BrettHallen/Rhythm_Keyboard/Images/Rhythm_Keyboard_Display.jpeg

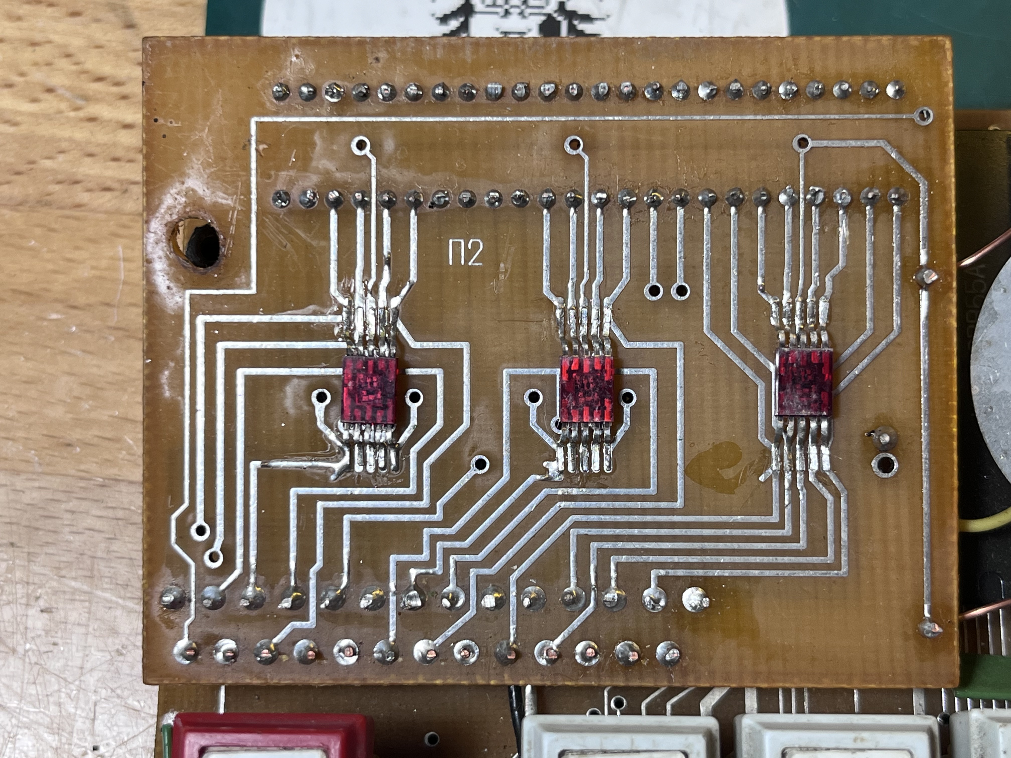
Images/Rhythm_Keyboard_Display.jpeg
