BrettHallen/Rhythm_Keyboard/Images/Rhythm_Keyboard_Expansion.jpeg

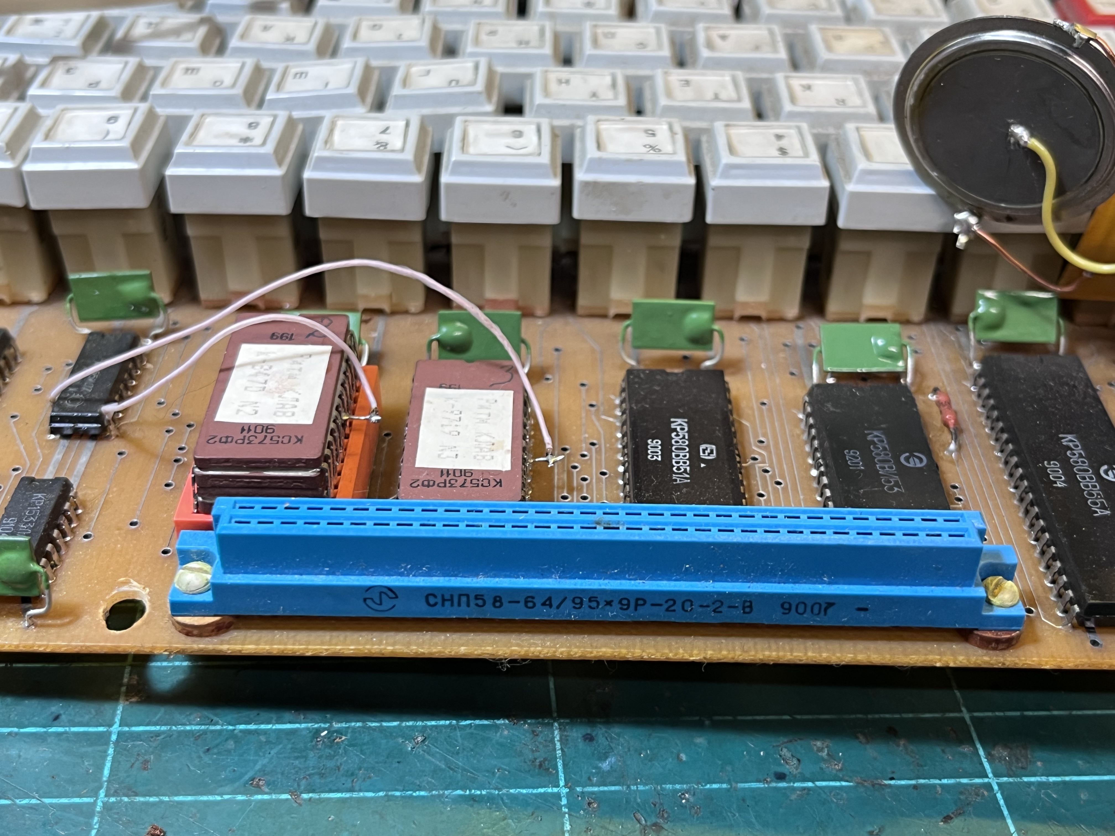
Images/Rhythm_Keyboard_Expansion.jpeg
