BrettHallen/Rhythm_Keyboard/Images/Rhythm_Keyboard_Motherboard01a.jpeg

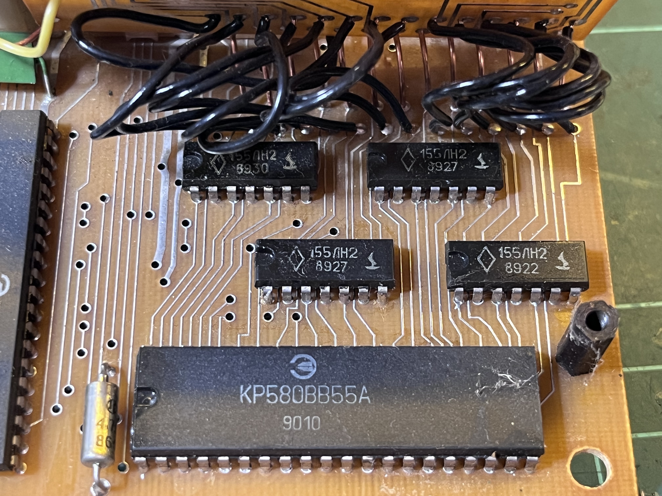
Images/Rhythm_Keyboard_Motherboard01a.jpeg
