BrettHallen/Rhythm_Keyboard/Images/Rhythm_Keyboard_Motherboard04.jpeg

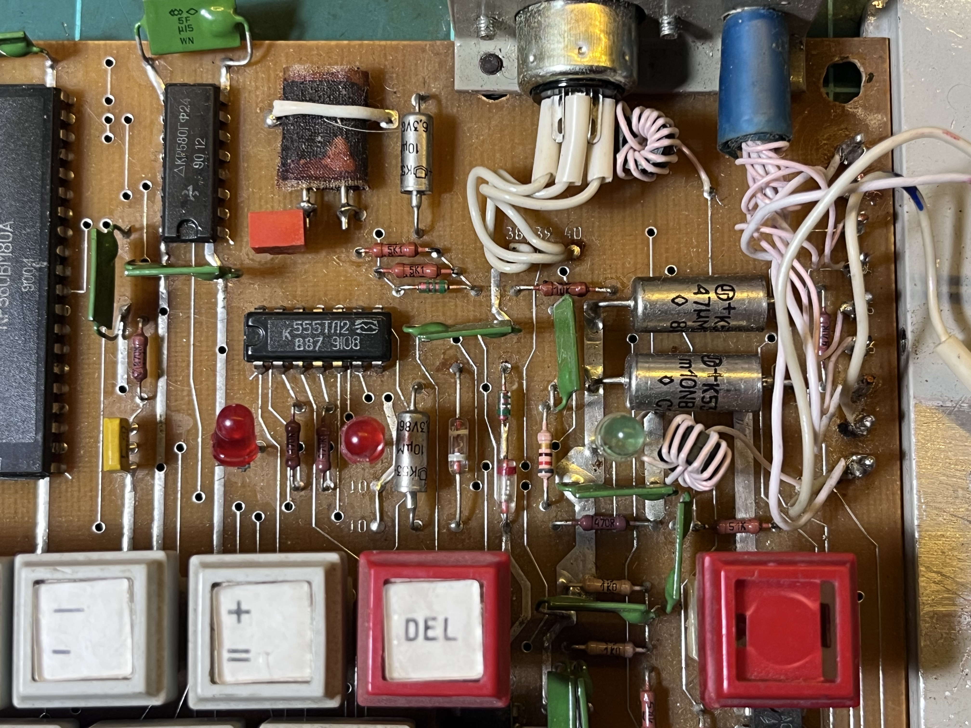
Images/Rhythm_Keyboard_Motherboard04.jpeg
