BrettHallen/Rhythm_Keyboard/Images/Rhythm_Keyboard_Motherboard05.jpeg

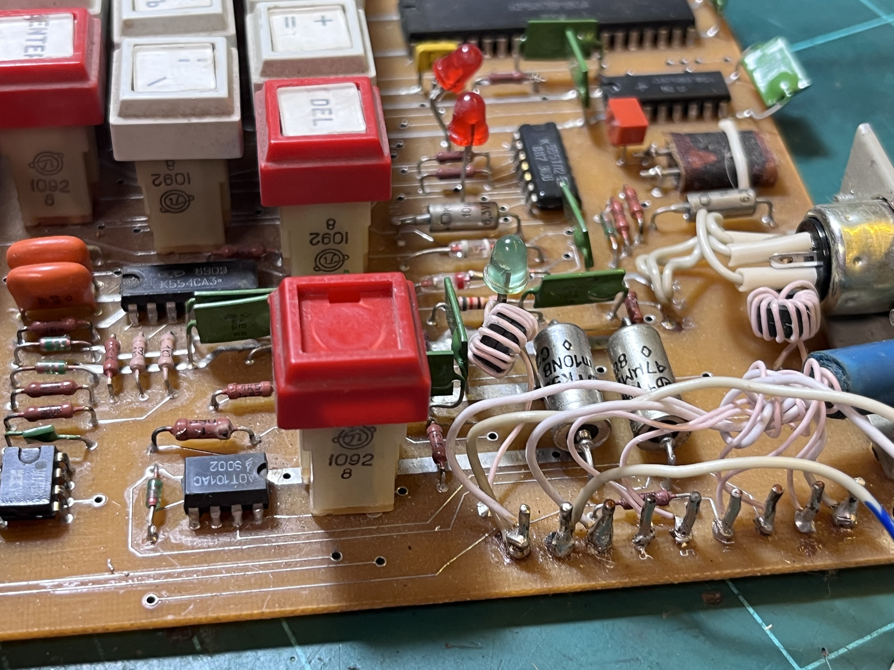
Images/Rhythm_Keyboard_Motherboard05.jpeg
