BrettHallen/Rhythm_Keyboard/Images/Rhythm_Keyboard_Motherboard06.jpeg

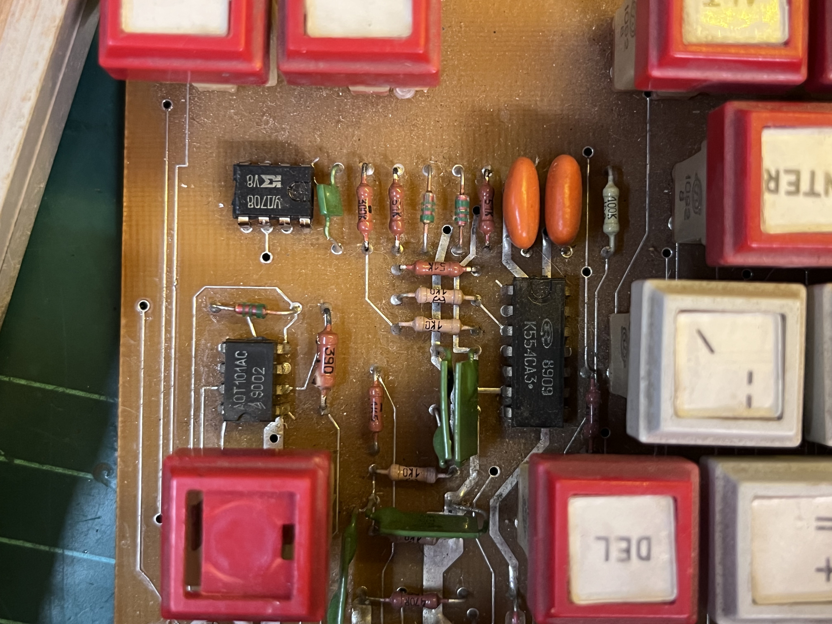
Images/Rhythm_Keyboard_Motherboard06.jpeg
