BrettHallen/Rhythm_Keyboard/Images/Rhythm_Keyboard_Motherboard07.jpeg

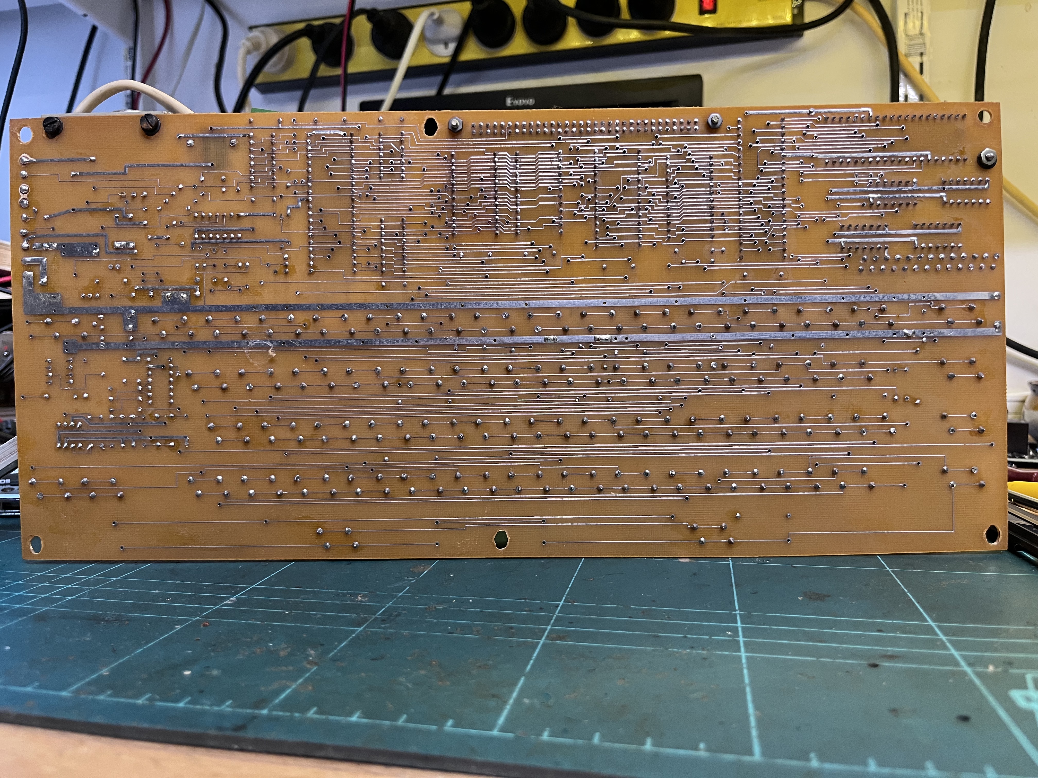
Images/Rhythm_Keyboard_Motherboard07.jpeg
