BrettHallen/Rhythm_Keyboard/Images/Rhythm_Keyboard_Motherboard08.jpeg

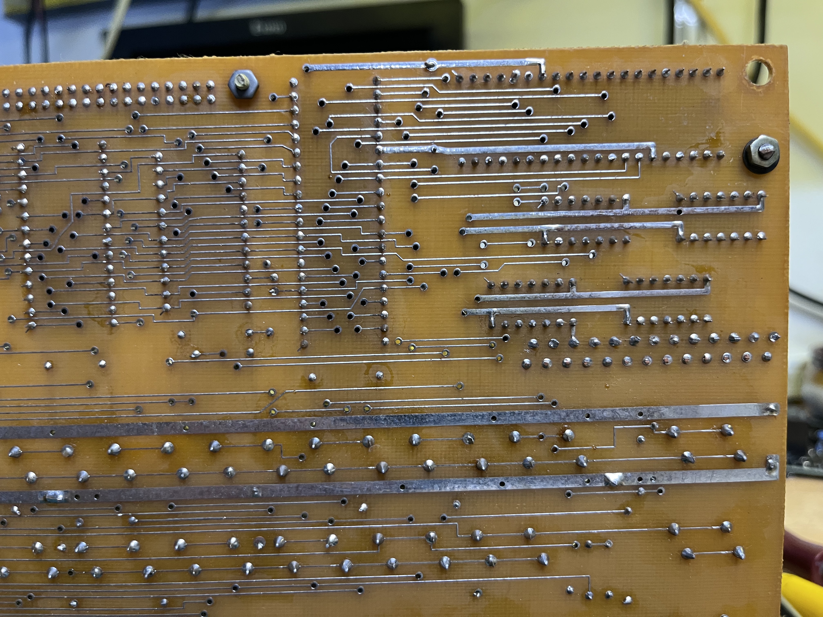
Images/Rhythm_Keyboard_Motherboard08.jpeg
