BrettHallen/Rhythm_Keyboard/Images/Rhythm_Keyboard_Motherboard11.jpeg

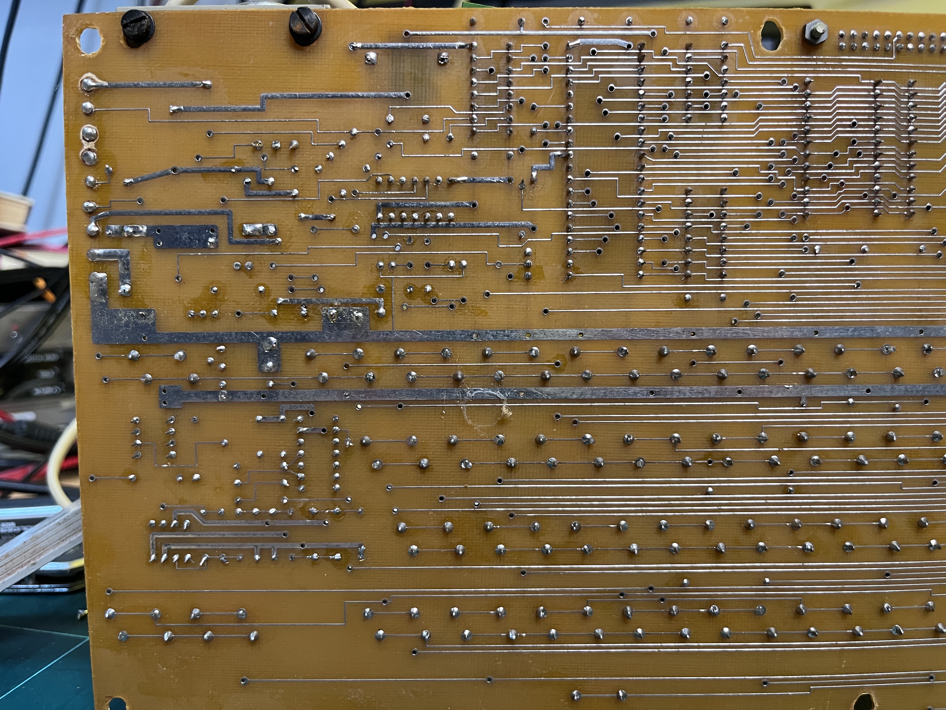
Images/Rhythm_Keyboard_Motherboard11.jpeg
