BrettHallen/Rhythm_Keyboard/Images/Rhythm_Keyboard_ROM_N2.jpeg

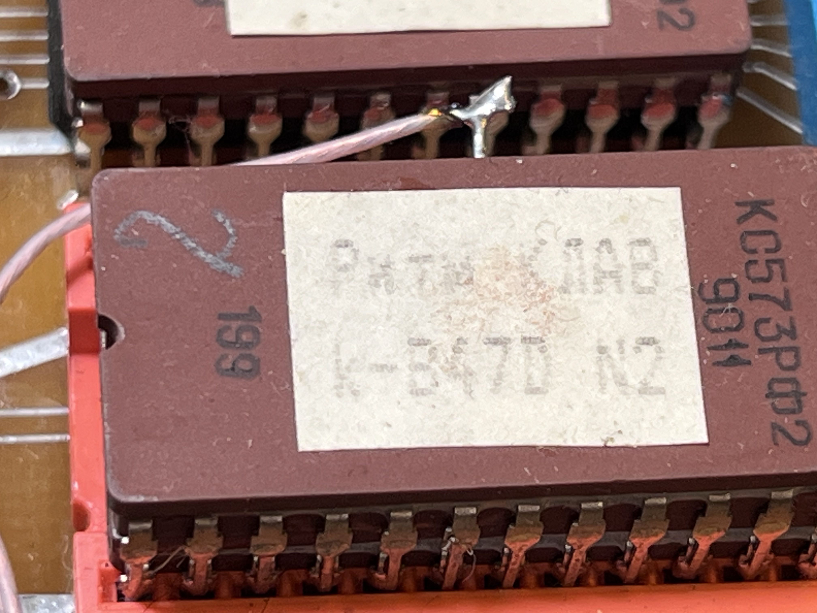
Images/Rhythm_Keyboard_ROM_N2.jpeg
