BrettHallen/Rhythm_Keyboard/Images/Rhythm_Keyboard_ROM_Select.jpeg

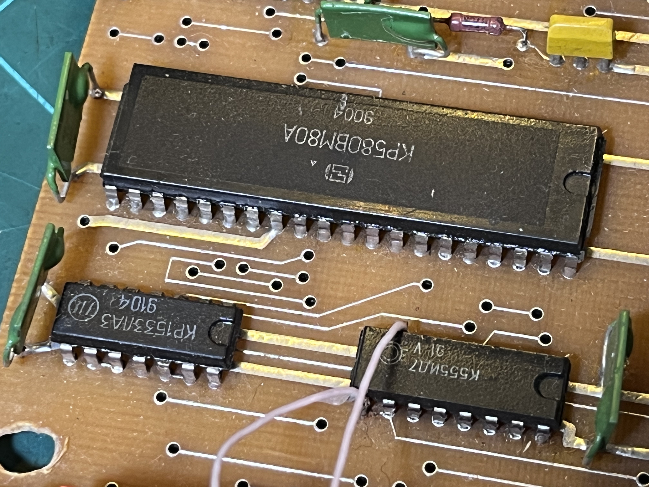
Images/Rhythm_Keyboard_ROM_Select.jpeg
