BrettHallen/Rhythm_Keyboard/Images/Rhythm_Keyboard_ROMs1.jpeg

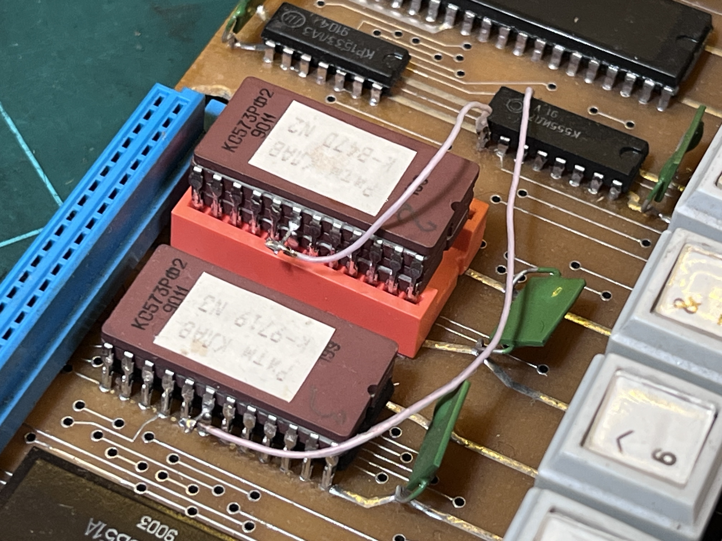
Images/Rhythm_Keyboard_ROMs1.jpeg
