BrettHallen/Rhythm_Keyboard/Images/Rhythm_Keyboard_Speaker_Transistor.jpeg

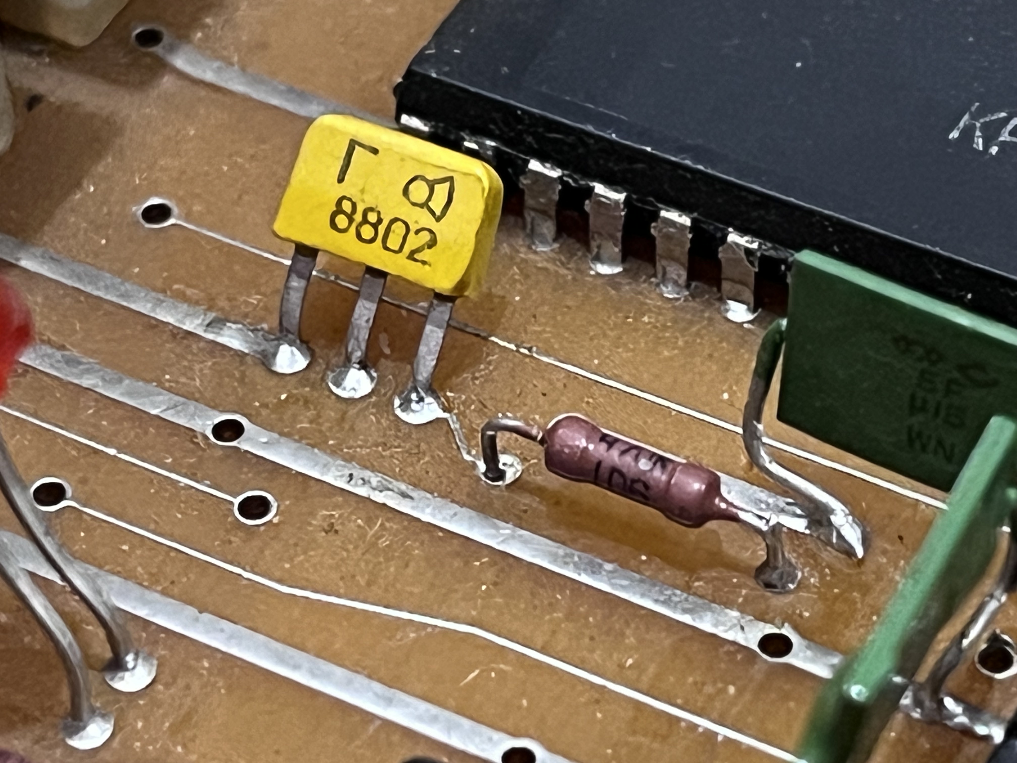
Images/Rhythm_Keyboard_Speaker_Transistor.jpeg
