BrettHallen/Rhythm_Keyboard/Images/Rhythm_Keyboard_SRAM.jpeg

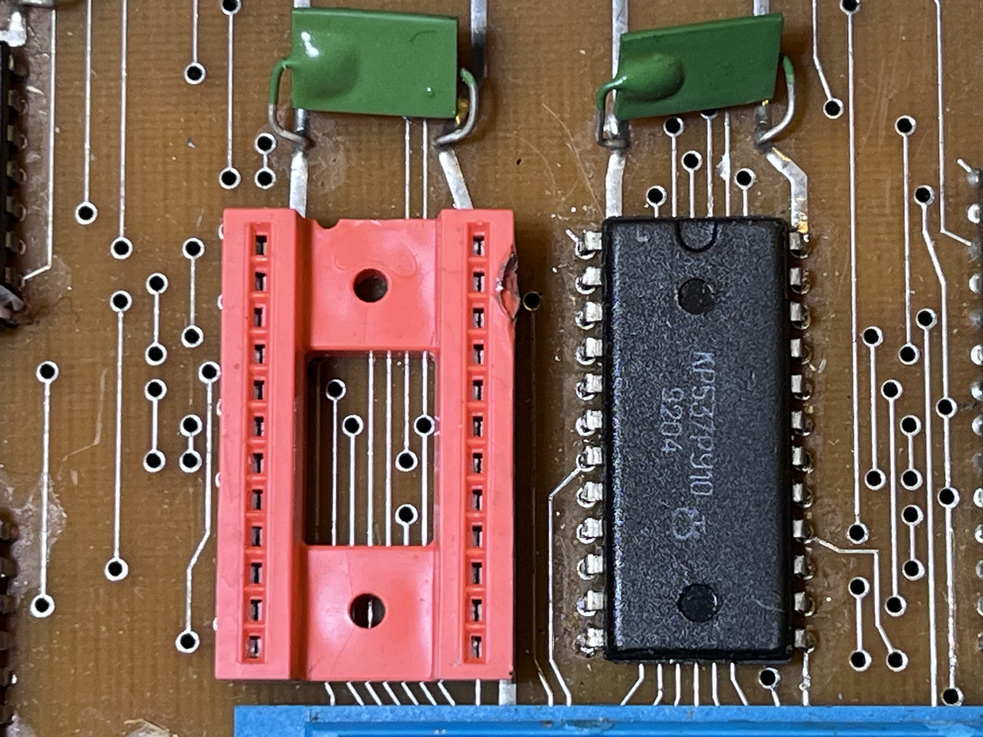
Images/Rhythm_Keyboard_SRAM.jpeg
