BrettHallen/Rhythm_Keyboard/ROMs/RITM_KLAV_N1.ASM

0000 c3 b4 39		jmp 39b4h
0003 f3      		di 
0004 31 00 10		lxi sp, 1000h
0007 3e 98   		mvi a, 98h
0009 32 03 18		sta 1803h
000c 3e 80   		mvi a, 80h
000e 32 03 28		sta 2803h
0011 3e 36   		mvi a, 36h
0013 32 03 20		sta 2003h
0016 21 0d 00		lxi h, 000dh
0019 7d      		mov a, l 
001a 32 00 20		sta 2000h
001d 7c      		mov a, h 
001e 32 00 20		sta 2000h
0021 3e 76   		mvi a, 76h
0023 32 03 20		sta 2003h
0026 21 52 03		lxi h, 0352h
0029 7d      		mov a, l 
002a 32 01 20		sta 2001h
002d 7c      		mov a, h 
002e 32 01 20		sta 2001h
0031 3e 00   		mvi a, 00h
0033 32 05 08		sta 0805h
0036 32 06 08		sta 0806h
0039 32 0b 08		sta 080bh
003c 32 0c 08		sta 080ch
003f 32 0d 08		sta 080dh
0042 3e ff   		mvi a, ffh
0044 32 01 28		sta 2801h
0047 32 00 28		sta 2800h
004a 32 02 28		sta 2802h
004d 3e ff   		mvi a, ffh
004f 32 12 08		sta 0812h
0052 32 02 18		sta 1802h
0055 cd 02 01		call 0102h
0058 3a 01 10		lda 1001h
005b e6 02   		ani 02h
005d ca 6b 00		jz 006bh
0060 3a 00 10		lda 1000h
0063 fe 0d   		cpi 0dh
0065 c2 6b 00		jnz 006bh
0068 c3 a7 00		jmp 00a7h
006b cd 94 03		call 0394h
006e fe 01   		cpi 01h
0070 c2 58 00		jnz 0058h
0073 78      		mov a, b 
0074 fe 45   		cpi 45h
0076 ca 81 00		jz 0081h
0079 fe 65   		cpi 65h
007b ca 81 00		jz 0081h
007e c3 58 00		jmp 0058h
0081 cd 7c 05		call 057ch
0084 cd 77 07		call 0777h
0087 e6 20   		ani 20h
0089 c2 58 00		jnz 0058h
008c 3e 0e   		mvi a, 0eh
008e cd b1 01		call 01b1h
0091 fe 00   		cpi 00h
0093 c2 a1 00		jnz 00a1h
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
07cd 3e 00   		mvi a, 00h
07cf 32 05 08		sta 0805h
07d2 32 06 08		sta 0806h
07d5 c9      		ret 
07d6 cd 1f 06		call 061fh
07d9 cd 28 06		call 0628h
07dc fe 02   		cpi 02h
07de ca 7a 06		jz 067ah
07e1 cd 3d 06		call 063dh
07e4 d2 18 30		jnc 3018h
07e7 fe 61   		cpi 61h
07e9 ca 09 30		jz 3009h
07ec fe 62   		cpi 62h
07ee ca 0e 30		jz 300eh
07f1 fe 64   		cpi 64h
07f3 ca 13 30		jz 3013h
07f6 cd 55 06		call 0655h
07f9 c3 d9 07		jmp 07d9h
07fc c3 09 30		jmp 3009h
07ff 00      		nop 
