BrettHallen/Rhythm_Keyboard/ROMs/RITM_KLAV_N2.ASM

0000 ff      		rst 7 
0001 00      		nop 
0002 ff      		rst 7 
0003 00      		nop 
0004 ff      		rst 7 
0005 00      		nop 
0006 ff      		rst 7 
0007 00      		nop 
0008 ff      		rst 7 
0009 3e 0a   		mvi a, 0ah
000b c3 1a 30		jmp 301ah
000e 3e 0b   		mvi a, 0bh
0010 c3 1a 30		jmp 301ah
0013 3e 0d   		mvi a, 0dh
0015 c3 1a 30		jmp 301ah
0018 d6 30   		sui 30h
001a 32 07 08		sta 0807h
001d cd a6 06		call 06a6h
0020 32 02 28		sta 2802h
0023 3a 07 08		lda 0807h
0026 fe 02   		cpi 02h
0028 ca 65 30		jz 3065h
002b cd 1f 06		call 061fh
002e cd 28 06		call 0628h
0031 fe 02   		cpi 02h
0033 ca 7a 06		jz 067ah
0036 cd 32 06		call 0632h
0039 da 2e 30		jc 302eh
003c d6 30   		sui 30h
003e 32 08 08		sta 0808h
0041 cd a6 06		call 06a6h
0044 32 00 28		sta 2800h
0047 cd 1f 06		call 061fh
004a 3a 07 08		lda 0807h
004d fe 03   		cpi 03h
004f ca 8f 30		jz 308fh
0052 cd 28 06		call 0628h
0055 fe 01   		cpi 01h
0057 ca 6d 30		jz 306dh
005a fe 02   		cpi 02h
005c ca 7a 06		jz 067ah
005f cd 55 06		call 0655h
0062 c3 52 30		jmp 3052h
0065 3e 00   		mvi a, 00h
0067 32 08 08		sta 0808h
006a c3 41 30		jmp 3041h
006d 3a 07 08		lda 0807h
0070 07      		rlc 
0071 07      		rlc 
0072 07      		rlc 
0073 07      		rlc 
0074 47      		mov b, a 
0075 3a 08 08		lda 0808h
0078 b0      		ora b 
0079 32 0b 08		sta 080bh
007c 3e 00   		mvi a, 00h
007e 32 0c 08		sta 080ch
0081 3e 06   		mvi a, 06h
0083 cd 3a 03		call 033ah
0086 3a 0b 08		lda 080bh
0089 cd 3a 03		call 033ah
008c c3 6e 05		jmp 056eh
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
07b5 fe 0f   		cpi 0fh
07b7 c2 ae 37		jnz 37aeh
07ba 7e      		mov a, m 
07bb b9      		cmp c 
07bc ca d1 37		jz 37d1h
07bf 3e 4b   		mvi a, 4bh
07c1 32 1f 08		sta 081fh
07c4 3e 43   		mvi a, 43h
07c6 32 20 08		sta 0820h
07c9 3e 3f   		mvi a, 3fh
07cb 32 21 08		sta 0821h
07ce c3 d4 37		jmp 37d4h
07d1 c3 e5 38		jmp 38e5h
07d4 cd 56 37		call 3756h
07d7 cd 77 07		call 0777h
07da e6 30   		ani 30h
07dc c2 c0 36		jnz 36c0h
07df 3e 0a   		mvi a, 0ah
07e1 cd 3a 03		call 033ah
07e4 c3 03 00		jmp 0003h
07e7 3e 0a   		mvi a, 0ah
07e9 cd 3a 03		call 033ah
07ec c3 03 00		jmp 0003h
07ef 21 b8 0b		lxi h, 0bb8h
07f2 51      		mov d, c 
07f3 cd c6 38		call 38c6h
07f6 d8      		rc 
07f7 79      		mov a, c 
07f8 fe de   		cpi deh
07fa d2 ef 37		jnc 37efh
07fd fe 05   		cpi 05h
